mmswflow-upb/MA-Project/project-files/KiCAD Files/MicroProject.kicad_pcb

## KiCad design kicad/battery.kicad_sch

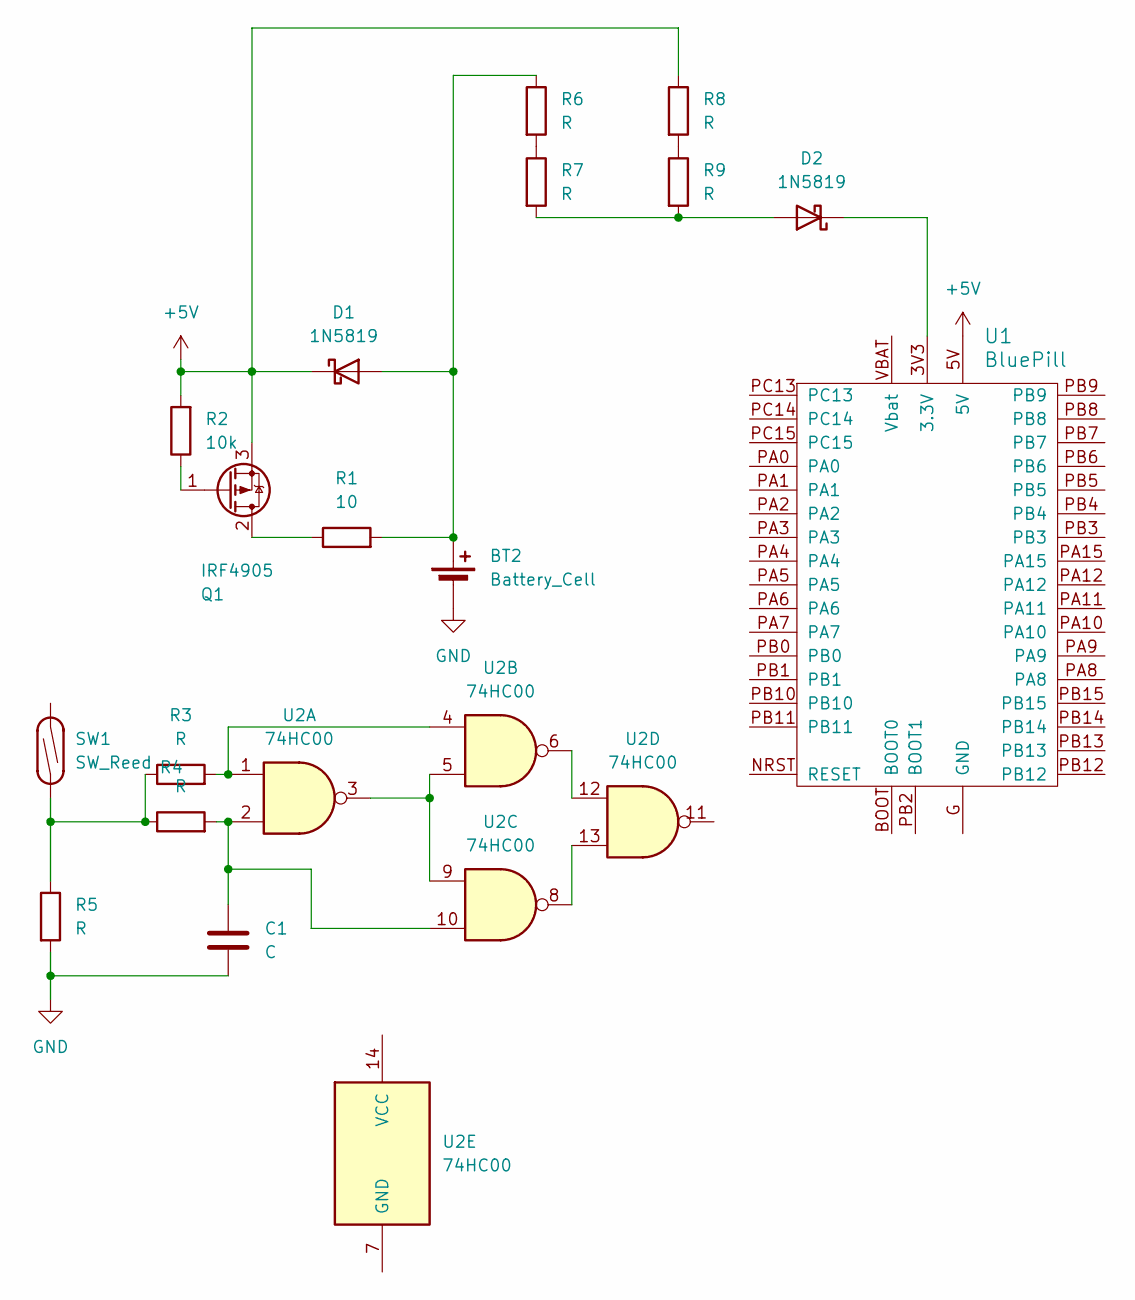
[picture p9: schematic battery.kicad_sch]

Parts:
BT2: Battery_Cell
C1: C
D1, D2: 1N5819; D_DO-41_SOD81_P10.16mm_Horizontal
Q1: IRF4905; TO-220-3_Vertical
R1: 10
R2: 10k
R3, R4, R5, R6, R7, R8, R9: R
SW1: SW_Reed
U1: BluePill; blue_pill
U2: 74HC00

Connections:
+5V: D1.1 (K), Q1.3 (S), R2.2, R8.1, U1.5V
GND: BT2.2 (-), C1.1, R5.2
unnamed: BT2.1 (+), D1.2 (A), R1.2, R6.1
unnamed: C1.2, R4.2, U2.2, U2.10
unnamed: D2.1 (K), U1.3V3 (3.3V)
unnamed: D2.2 (A), R7.2, R9.2
unnamed: Q1.1 (G), R2.1
unnamed: Q1.2 (D), R1.1
unnamed: R3.1, R4.1, R5.1, SW1.1
unnamed: R3.2, U2.1, U2.4
unnamed: R6.2, R7.1
unnamed: R8.2, R9.1
unnamed: U2.3, U2.5, U2.9
unnamed: U2.6, U2.12
unnamed: U2.8, U2.13
